thewiz4real-ops/DIY_Reflow_Hotplate/media/video/README.md

# Video

The YouTube link for this project is stored in `youtube-link.txt`.

Current video:

- `https://youtu.be/tEUVSpoKs-g`
