thewiz4real-ops/DIY_Reflow_Hotplate/hardware/controller-board/production-pcb/README.md

# Production PCB version

The current build uses perfboard.
