thewiz4real-ops/DIY_Reflow_Hotplate/hardware/controller-board/schematic/README.md

# Schematic

This folder groups schematic-related material for the controller side of the project.

For the current pin summary and wiring references, see:

- `../../wiring/connector_map.md`
- `../../../docs/03_electronics_and_wiring.md`
