thewiz4real-ops/DIY_Reflow_Hotplate/hardware/enclosure/stl/README.md

The enclosure source files in this repo are stored in `../cad/brain-box/`.
