thewiz4real-ops/DIY_Reflow_Hotplate/mechanical/armature/cad/README.md

# Armature CAD

The armature fabrication process is described in `docs/02_mechanical_build.md` and shown in the YouTube video.
