thewiz4real-ops/DIY_Reflow_Hotplate/hardware/controller-board/perfboard/README.md

# Perfboard version

Document:
- board photos
- jumper wire method
- JST connector placement
- MOSFET / relay drive section
- sensor section
- power section
