thewiz4real-ops/DIY_Reflow_Hotplate/mechanical/armature/cnc/README.md

# CNC notes for the armature

CAM was prepared in Kiri:Moto.

Original process summary:
- export CAD
- import into Kiri:Moto
- set tool and material thickness
- generate toolpaths
- check preview
- export G-code
- use plywood sacrificial board
- double-sided tape under aluminum
- clamps on top
- cut in multiple passes
